Tom-Sloan/pillbox/Pillbox Software/Pillbox/3d Prints/3MF/slot45Degrees.3mf

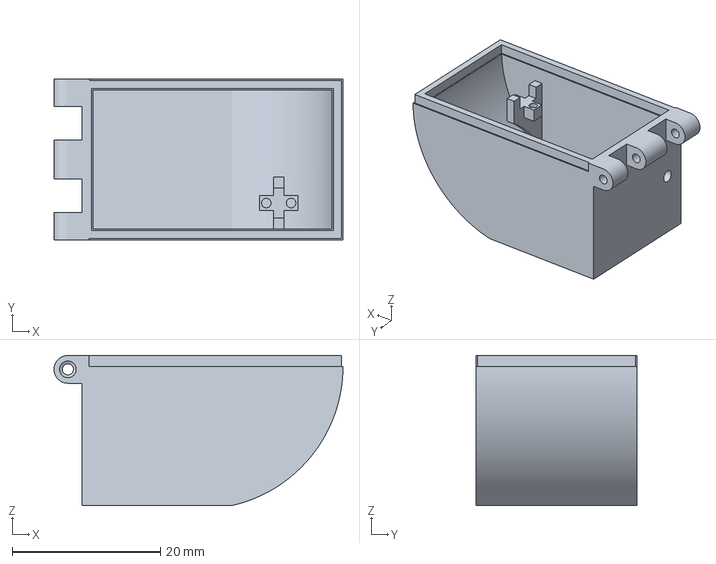
[picture p12: CAD file, 2021-03-13]
Pillbox Software/Pillbox/3d Prints/3MF/slot45Degrees.3mf
39.0 x 21.8 x 20.2 mm
