Tom-Sloan/pillbox/Pillbox Software/Pillbox/3d Prints/3MF/Axel.3mf

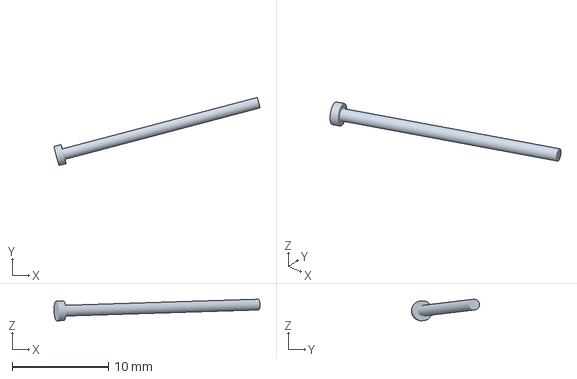
[picture p13: CAD file, 2021-03-09]
Pillbox Software/Pillbox/3d Prints/3MF/Axel.3mf
21.4 x 7.08 x 2.26 mm
