Tom-Sloan/pillbox/Pillbox Software/Pillbox/Feather_Bluetooth.ino

/*---------------ADAFRUIT functions from BLEUART example-------------------------*/
void initBLE()
{
  // Setup the BLE LED to be enabled on CONNECT
  // Note: This is actually the default behaviour, but provided
  // here in case you want to control this LED manually via PIN 19
  Bluefruit.autoConnLed(true);

  // Config the peripheral connection with maximum bandwidth
  // more SRAM required by SoftDevice
  // Note: All config***() function must be called before begin()
  Bluefruit.configPrphBandwidth(BANDWIDTH_MAX);

  Bluefruit.begin();
  Bluefruit.setTxPower(4);    // Check bluefruit.h for supported values
  Bluefruit.setName("Pillbox");
  //Bluefruit.setName(getMcuUniqueID()); // useful testing with multiple central connections
  Bluefruit.Periph.setConnectCallback(connect_callback);
  Bluefruit.Periph.setDisconnectCallback(disconnect_callback);

  // To be consistent OTA DFU should be added first if it exists
  bledfu.begin();

  // Configure and Start Device Information Service
  bledis.setManufacturer("Adafruit Industries");
  bledis.setModel("Bluefruit Feather52");
  bledis.begin();

  // Configure and Start BLE Uart Service
  bleuart.begin();

  // Start BLE Battery Service
  blebas.begin();
  blebas.write(100);

  // Set up and start advertising
  startAdv();

  Serial.println("Please use Adafruit's Bluefruit LE app to connect in UART mode");
  Serial.println("Once connected, enter character(s) that you wish to send");
}


void startAdv(void)
{
  // Advertising packet
  Bluefruit.Advertising.addFlags(BLE_GAP_ADV_FLAGS_LE_ONLY_GENERAL_DISC_MODE);
  Bluefruit.Advertising.addTxPower();

  // Include bleuart 128-bit uuid
  Bluefruit.Advertising.addService(bleuart);

  // Secondary Scan Response packet (optional)
  // Since there is no room for 'Name' in Advertising packet
  Bluefruit.ScanResponse.addName();

  /* Start Advertising
     - Enable auto advertising if disconnected
     - Interval:  fast mode = 20 ms, slow mode = 152.5 ms
     - Timeout for fast mode is 30 seconds
     - Start(timeout) with timeout = 0 will advertise forever (until connected)

     For recommended advertising interval
     https://developer.apple.com/library/content/qa/qa1931/_index.html
  */
  Bluefruit.Advertising.restartOnDisconnect(true);
  Bluefruit.Advertising.setInterval(32, 244);    // in unit of 0.625 ms
  Bluefruit.Advertising.setFastTimeout(30);      // number of seconds in fast mode
  Bluefruit.Advertising.start(0);                // 0 = Don't stop advertising after n seconds
}


// callback invoked when central connects
void connect_callback(uint16_t conn_handle)
{
  // Get the reference to current connection
  BLEConnection* connection = Bluefruit.Connection(conn_handle);

  char central_name[32] = { 0 };
  connection->getPeerName(central_name, sizeof(central_name));

  Serial.print("Connected to ");
  Serial.println(central_name);
}

/**
   Callback invoked when a connection is dropped
   @param conn_handle connection where this event happens
   @param reason is a BLE_HCI_STATUS_CODE which can be found in ble_hci.h
*/
void disconnect_callback(uint16_t conn_handle, uint8_t reason)
{
  (void) conn_handle;
  (void) reason;

  Serial.println();
  Serial.print("Disconnected, reason = 0x"); Serial.println(reason, HEX);
}
/*---------------ADAFRUIT functions from BLEUART example end-------------------------*/

//used for row detection. doesn't do much otherwise
void processMessage(String dataReceived)
{
  if (dataReceived.charAt(2)-'0' != numRows){
    int oldNumRows = numRows;
    numRows = dataReceived.charAt(2)-'0';
    SD.remove("setup.txt");
    
    File file_read = SD.open("setup.txt", FILE_WRITE);
    file_read.print(dataReceived);
    file_read.close();

    rowChange(oldNumRows);
  }else{
    String tmp = "Message received: " + dataReceived;
    Serial.println(tmp);   
  }
}
